uhppoted/uhppoted-breakout/Rev.0/firmware/core/src/sys.c

#include <malloc.h>
#include <stdio.h>
#include <stdlib.h>
#include <string.h>
#include <unistd.h>

#include <hardware/flash.h>
#include <hardware/watchdog.h>
#include <pico/stdlib.h>
#include <pico/sync.h>
#include <pico/unique_id.h>

#include <RTC.h>
#include <SSMP.h>
#include <U2.h>
#include <U3.h>
#include <breakout.h>
#include <cli.h>
#include <log.h>
#include <mempool.h>
#include <settings.h>
#include <sys.h>
#include <types/buffer.h>

#define LOGTAG "SYS"
#define PRINT_QUEUE_SIZE 64

extern const char *TERMINAL_QUERY_STATUS;
const int32_t FLUSH = 1000;              // ms
const uint32_t MODE_CLI_TIMEOUT = 15000; // ms

const uint32_t MSG = 0xf0000000;
const uint32_t MSG_DEBUG = 0x00000000;
const uint32_t MSG_WIO = 0x10000000;
const uint32_t MSG_SWIPE = 0x20000000;
const uint32_t MSG_KEYCODE = 0x30000000;
const uint32_t MSG_U3 = 0x40000000;
const uint32_t MSG_RX = 0x50000000;
const uint32_t MSG_SAVE = 0x60000000;
const uint32_t MSG_EVENT = 0x70000000;
const uint32_t MSG_TTY = 0xb0000000;
const uint32_t MSG_TRACE = 0xc0000000;
const uint32_t MSG_LOG = 0xd0000000;
const uint32_t MSG_WATCHDOG = 0xe0000000;
const uint32_t MSG_TICK = 0xf0000000;

extern queue_t queue;

extern struct {
    queue_t queue;
    mutex_t guard;
} I2C0;

extern void syserr_tick();

struct {
    repeating_timer_t timer;
    uint32_t ticks;
    mode mode;
    bool reboot;

    struct {
        mutex_t lock;
        bool connected;
        int head;
        int tail;
        char list[PRINT_QUEUE_SIZE][128];
    } queue;

    struct {
        absolute_time_t touched;
    } cli;

    struct {
        bool RTC;
        float interval;
        absolute_time_t touched;
        repeating_timer_t timer;
    } trace;

    mutex_t guard;
} SYSTEM = {
    .ticks = 0,
    .mode = MODE_NONE,
    .reboot = false,
    .queue = {
        .connected = false,
        .head = 0,
        .tail = 0,
    },

    .cli = {
        .touched = 0,
    },

    .trace = {
        .RTC = true,
        .interval = (float)TRACE,
        .touched = 0,
    },
};

void _push(const char *);
void _flush();
void _print(const char *);
bool _tick(repeating_timer_t *t);
bool _trace(repeating_timer_t *t);

bool sysinit() {
    mutex_init(&SYSTEM.guard);
    mutex_init(&SYSTEM.queue.lock);

    // ... restore settings
    // FIXME settings_restore();

    // ... USB/UART0 mode
    if (strcasecmp(MODE, "cli") == 0) {
        SYSTEM.mode = MODE_UNKNOWN; // NTS: will be set to MODE_CLI if/when terminal is connected
    } else if (strcasecmp(MODE, "log") == 0) {
        SYSTEM.mode = MODE_LOG;
    } else {
        SYSTEM.mode = MODE_NONE;
    }

    // ... system tick
    if (!add_repeating_timer_ms(1000, _tick, &SYSTEM, &SYSTEM.timer)) {
        return false;
    }

    // ... tracing
    if (!add_repeating_timer_ms(250, _trace, &SYSTEM, &SYSTEM.trace.timer)) {
        return false;
    }

    return true;
}

bool _tick(repeating_timer_t *t) {
    SYSTEM.ticks++;

    message qmsg = {
        .message = MSG_TICK,
        .tag = MESSAGE_NONE,
    };

    push(qmsg);
    syserr_tick();

    return true;
}

bool _trace(repeating_timer_t *t) {
    message m = {
        .message = MSG_TRACE,
        .tag = MESSAGE_NONE,
    };

    push(m);

    return true;
}

/* Checks memory usage, etc.
 *
 */
void syscheck() {
    // ... check memory usage
    uint32_t heap = get_total_heap();
    uint32_t available = get_free_heap();
    float used = 1.0 - ((float)available / (float)heap);

    if (used > 0.5 && !syserr_get(ERR_MEMORY)) {
        syserr_set(ERR_MEMORY, LOGTAG, "memory usage %d%%", (int)(100.0 * used));
    }

    // ... kick watchdog
    if (!SYSTEM.reboot) {
        message qmsg = {
            .message = MSG_WATCHDOG,
            .tag = MESSAGE_NONE,
        };

        push(qmsg);
    }
}

/* Sets sys.reboot flag to inhibit watchdog reset.
 *
 */
void sys_reboot() {
    SYSTEM.reboot = true;
}

void sys_trace() {
    int64_t interval = (int64_t)(1000.0 * SYSTEM.trace.interval);
    absolute_time_t now = get_absolute_time();
    int64_t delta = absolute_time_diff_us(SYSTEM.trace.touched, now) / 1000;

    if (interval > 0 && delta >= interval) {
        uint16_t errors = syserr_bitmask();
        uint32_t heap = get_total_heap();
        uint32_t available = get_free_heap();
        float used = 1.0 - ((float)available / (float)heap);
        const char *watchdogged = syserr_get(ERR_WATCHDOG) ? "** watchdog **" : "";

        debugf(LOGTAG, "trace  ticks:%-5u queue:%u  I2C0:%u  heap:%u  heap:%u  used:%.1f%%  errors:%04x  %s",
               SYSTEM.ticks,
               queue_get_level(&queue),
               queue_get_level(&I2C0.queue),
               heap,
               available,
               100.0f * used,
               errors,
               watchdogged);

        SYSTEM.trace.touched = get_absolute_time();
    }
}

int sys_id(char *ID, int N) {
    pico_unique_board_id_t board_id;

    pico_get_unique_board_id(&board_id);

    snprintf(ID, N, "%02x%02x%02x%02x%02x%02x%02x%02x",
             board_id.id[0],
             board_id.id[1],
             board_id.id[2],
             board_id.id[3],
             board_id.id[4],
             board_id.id[5],
             board_id.id[6],
             board_id.id[7]);

    return N < 16 ? N : 16;
}

mode get_mode() {
    switch (SYSTEM.mode) {
    case MODE_NONE:
        return MODE_NONE;

    case MODE_LOG:
        return MODE_LOG;

    case MODE_CLI:
        return MODE_CLI;

    case MODE_UNKNOWN:
        return MODE_UNKNOWN;

    default:
        return MODE_NONE;
    }
}

void set_mode(mode mode) {
    if (SYSTEM.mode == MODE_NONE) {
        return;
    }

    if (SYSTEM.mode != mode) {
        SYSTEM.mode = mode;

        // ... unblock queue
        if (mode == MODE_CLI) {
            SYSTEM.cli.touched = get_absolute_time();
            print("");
        }
    }
}

void stdout_connected(bool connected) {
    if (connected != SYSTEM.queue.connected) {
        SYSTEM.queue.connected = connected;
        if (connected) {
            print("");
        }
    }
}

void set_trace(float interval) {
    if (interval >= 0.0 && interval <= 300.0) {
        SYSTEM.trace.interval = interval;
    }
}

void set_trace_RTC(bool enabled) {
    SYSTEM.trace.RTC = enabled;
}

void dispatch(uint32_t v) {
    if ((v & MSG) == MSG_DEBUG) {
        debugf(LOGTAG, "... debug??");
    }

    if ((v & MSG) == MSG_WIO) {
        U2_wio(v & 0x0000ffff);
    }

    if ((v & MSG) == MSG_SWIPE) {
        swipe *swipe = (struct swipe *)(SRAM_BASE | (v & 0x0fffffff));

        infof(LOGTAG, "READER %d  CARD %s", swipe->door, swipe->card);

        switch (swipe->door) {
        case 1:
            SSMP_trap(EVENT_DOOR_1_SWIPE, swipe->card);
            break;

        case 2:
            SSMP_trap(EVENT_DOOR_2_SWIPE, swipe->card);
            break;

        case 3:
            SSMP_trap(EVENT_DOOR_3_SWIPE, swipe->card);
            break;

        case 4:
            SSMP_trap(EVENT_DOOR_4_SWIPE, swipe->card);
            break;
        }

        swipe_free(swipe);
    }

    if ((v & MSG) == MSG_KEYCODE) {
        swipe *swipe = (struct swipe *)(SRAM_BASE | (v & 0x0fffffff));

        infof(LOGTAG, "KEYPAD %d  KEYCODE %s", swipe->door, swipe->code);

        switch (swipe->door) {
        case 1:
            SSMP_trap(EVENT_DOOR_1_KEYCODE, swipe->code);
            break;

        case 2:
            SSMP_trap(EVENT_DOOR_2_KEYCODE, swipe->code);
            break;

        case 3:
            SSMP_trap(EVENT_DOOR_3_KEYCODE, swipe->code);
            break;

        case 4:
            SSMP_trap(EVENT_DOOR_4_KEYCODE, swipe->code);
            break;
        }

        swipe_free(swipe);
    }

    if ((v & MSG) == MSG_U3) {
        U3_process(v & 0x000000ff);
    }

    if ((v & MSG) == MSG_RX) {
        struct circular_buffer *b = (struct circular_buffer *)(SRAM_BASE | (v & 0x0fffffff));

        SSMP_rx(b);
    }

    if ((v & MSG) == MSG_TTY) {
        struct circular_buffer *b = (struct circular_buffer *)(SRAM_BASE | (v & 0x0fffffff));

        cli_rx(b);
    }

    if ((v & MSG) == MSG_SAVE) {
        settings_save();
    }

    if ((v & MSG) == MSG_TRACE) {
        sys_trace();

        if (SYSTEM.trace.RTC) {
            RTC_trace();
        }
    }

    if ((v & MSG) == MSG_TICK) {
        syscheck();
        sys_tick();

        // ... MODE_CLI timeout?
        if (get_mode() == MODE_CLI || get_mode() == MODE_UNKNOWN) {
            absolute_time_t now = get_absolute_time();
            int64_t delta = absolute_time_diff_us(SYSTEM.cli.touched, now) / 1000;

            if (llabs(delta) > MODE_CLI_TIMEOUT) {
                set_mode(MODE_UNKNOWN);
            }

            // ... ping terminal
            if (mutex_try_enter(&SYSTEM.guard, NULL)) {
                _print(TERMINAL_QUERY_STATUS);
                mutex_exit(&SYSTEM.guard);
            }
        }

        // ... bump log queue
        message qmsg = {
            .message = MSG_LOG,
            .tag = MESSAGE_NONE,
        };

        push(qmsg);
    }

    if ((v & MSG) == MSG_EVENT) {
        EVENT event = (EVENT)(v & 0x0fffffff);

        SSMP_trap(event, NULL);
    }

    if ((v & MSG) == MSG_LOG) {
        _flush();
    }

    if ((v & MSG) == MSG_WATCHDOG) {
        watchdog_update();
    }
}

void print(const char *msg) {
    switch (SYSTEM.mode) {
    case MODE_NONE:
        return;

    default:
        _push(msg);
    }
}

void _push(const char *msg) {
    if (mutex_try_enter(&SYSTEM.queue.lock, NULL)) {
        int head = SYSTEM.queue.head;
        int tail = SYSTEM.queue.tail;
        int next = (head + 1) % PRINT_QUEUE_SIZE;

        if (next == SYSTEM.queue.tail) {
            snprintf(SYSTEM.queue.list[tail++], 128, "...\n");
            tail %= PRINT_QUEUE_SIZE;

            snprintf(SYSTEM.queue.list[tail], 128, "...\n");

            SYSTEM.queue.tail = tail;
        }

        if (next != SYSTEM.queue.tail) {
            snprintf(SYSTEM.queue.list[head], 128, "%s", msg);
            SYSTEM.queue.head = next;
        }

        mutex_exit(&SYSTEM.queue.lock);
    }

    message qmsg = {
        .message = MSG_LOG,
        .tag = MESSAGE_NONE,
    };

    push(qmsg);
}

/* Flushes all pending messages to stdout.
 *
 */
void _flush() {
    if (SYSTEM.mode != MODE_LOG && SYSTEM.mode != MODE_CLI) {
        return;
    }

    if (SYSTEM.mode != MODE_LOG && SYSTEM.mode != MODE_CLI) {
        return;
    }

    if (!SYSTEM.queue.connected) {
        return;
    }

    if (mutex_try_enter(&SYSTEM.guard, NULL)) {
        if (mutex_try_enter(&SYSTEM.queue.lock, NULL)) {
            int head = SYSTEM.queue.head;
            int tail = SYSTEM.queue.tail;

            while (tail != head) {
                _print(SYSTEM.queue.list[tail++]);
                tail %= PRINT_QUEUE_SIZE;
            }

            SYSTEM.queue.tail = tail;
            mutex_exit(&SYSTEM.queue.lock);
        }

        mutex_exit(&SYSTEM.guard);
    }
}

/* Prints all of a message to stdout.
 *
 */
void _print(const char *msg) {
    int remaining = strlen(msg);
    int ix = 0;
    int N;

    while (remaining > 0) {
        if ((N = fwrite(&msg[ix], 1, remaining, stdout)) <= 0) {
            break;
        } else {
            remaining -= N;
            ix += N;
        }
    }

    fflush(stdout);
}

uint32_t get_total_heap() {
    extern char __StackLimit, __bss_end__;

    return &__StackLimit - &__bss_end__;
}

uint32_t get_free_heap() {
    extern char __StackLimit, __bss_end__;

    uint32_t total = &__StackLimit - &__bss_end__;
    struct mallinfo m = mallinfo();

    return total - m.uordblks;
}
