uhppoted/uhppoted-breakout/Rev.0/firmware/core/src/MIB.c

#include <stdio.h>
#include <stdlib.h>
#include <string.h>

#include <crypt/hash/djb2.h>

#include <MIB.h>
#include <RTC.h>
#include <SSMP.h>
#include <U3.h>
#include <U4.h>
#include <breakout.h>
#include <log.h>
#include <sys.h>

#define LOGTAG "MIB"

const struct {
    uint32_t hash;
    char *OID;
} MIB[] = {
    {.hash = HASH_MIB_BOARD_ID, .OID = MIB_BOARD_ID},
    {.hash = HASH_MIB_CONTROLLER_ID, .OID = MIB_CONTROLLER_ID},
    {.hash = HASH_MIB_CONTROLLER_VERSION, .OID = MIB_CONTROLLER_VERSION},
    {.hash = HASH_MIB_CONTROLLER_RELEASED, .OID = MIB_CONTROLLER_RELEASED},
    {.hash = HASH_MIB_CONTROLLER_DATETIME, .OID = MIB_CONTROLLER_DATETIME},
    {.hash = HASH_MIB_CONTROLLER_SYSERROR, .OID = MIB_CONTROLLER_SYSERROR},
    {.hash = HASH_MIB_CONTROLLER_SYSINFO, .OID = MIB_CONTROLLER_SYSINFO},
    {.hash = HASH_MIB_DOORS_1_UNLOCKED, .OID = MIB_DOORS_1_UNLOCKED},
    {.hash = HASH_MIB_DOORS_2_UNLOCKED, .OID = MIB_DOORS_2_UNLOCKED},
    {.hash = HASH_MIB_DOORS_3_UNLOCKED, .OID = MIB_DOORS_3_UNLOCKED},
    {.hash = HASH_MIB_DOORS_4_UNLOCKED, .OID = MIB_DOORS_4_UNLOCKED},
    {.hash = HASH_MIB_DOORS_1_OPEN, .OID = MIB_DOORS_1_OPEN},
    {.hash = HASH_MIB_DOORS_2_OPEN, .OID = MIB_DOORS_2_OPEN},
    {.hash = HASH_MIB_DOORS_3_OPEN, .OID = MIB_DOORS_3_OPEN},
    {.hash = HASH_MIB_DOORS_4_OPEN, .OID = MIB_DOORS_4_OPEN},
    {.hash = HASH_MIB_DOORS_1_BUTTON, .OID = MIB_DOORS_1_BUTTON},
    {.hash = HASH_MIB_DOORS_2_BUTTON, .OID = MIB_DOORS_2_BUTTON},
    {.hash = HASH_MIB_DOORS_3_BUTTON, .OID = MIB_DOORS_3_BUTTON},
    {.hash = HASH_MIB_DOORS_4_BUTTON, .OID = MIB_DOORS_4_BUTTON},
};

value MIB_get_boolean(const char *OID);

int64_t MIB_set_string(const char *OID, const char *s, int length, value *v);

value MIB_get(const char *OID) {
    uint32_t hash = djb2(OID);

    value v = {
        .tag = VALUE_UNKNOWN,
    };

    if (strcmp(OID, MIB_BOARD_ID) == 0) {
        char ID[32];
        int N = sys_id(ID, sizeof(ID));
        slice octets = {
            .capacity = 64,
            .length = N,
            .bytes = (char *)calloc(64, sizeof(uint8_t)),
        };

        memmove(octets.bytes, ID, N);

        v.tag = VALUE_OCTET_STRING;
        v.octets = octets;
    }

    if (strcmp(OID, MIB_CONTROLLER_ID) == 0) {
        v.tag = VALUE_UINT32;
        v.integer = CONTROLLER;
    }

    if (strcmp(OID, MIB_CONTROLLER_VERSION) == 0) {
        v.tag = VALUE_UINT16;
        v.integer = VERSION;
    }

    if (strcmp(OID, MIB_CONTROLLER_RELEASED) == 0) {
        slice octets = {
            .capacity = 32,
            .length = 0,
            .bytes = (char *)calloc(32, sizeof(uint8_t)),
        };

        int N = snprintf(octets.bytes, octets.capacity, "%s", RELEASED);
        if (N > 0) {
            octets.length = N < strlen(RELEASED) ? N : strlen(RELEASED);
        }

        v.tag = VALUE_OCTET_STRING;
        v.octets = octets;
    }

    if (strcmp(OID, MIB_CONTROLLER_DATETIME) == 0) {
        slice octets = {
            .capacity = 32,
            .length = 0,
            .bytes = (char *)calloc(32, sizeof(uint8_t)),
        };

        char date[16] = {0};
        char time[16] = {0};
        char datetime[32] = {0};

        RTC_get_date(date, sizeof(date));
        RTC_get_time(time, sizeof(time));

        snprintf(datetime, sizeof(datetime), "%s %s", date, time);

        int N = snprintf(octets.bytes, octets.capacity, "%s", datetime);
        if (N > 0) {
            octets.length = N < strlen(datetime) ? N : strlen(datetime);
        }

        v.tag = VALUE_OCTET_STRING;
        v.octets = octets;
    }

    if (strcmp(OID, MIB_CONTROLLER_SYSERROR) == 0) {
        v.tag = VALUE_UINT8;
        v.integer = (uint8_t)get_errors();
    }

    if (strcmp(OID, MIB_CONTROLLER_SYSINFO) == 0) {
        v.tag = VALUE_UINT8;
        v.integer = 0;
    }

    if (strcmp(OID, MIB_DOORS_1_UNLOCKED) == 0) {
        return MIB_get_boolean(OID);
    }

    if (strcmp(OID, MIB_DOORS_2_UNLOCKED) == 0) {
        return MIB_get_boolean(OID);
    }

    if (strcmp(OID, MIB_DOORS_3_UNLOCKED) == 0) {
        return MIB_get_boolean(OID);
    }

    if (strcmp(OID, MIB_DOORS_4_UNLOCKED) == 0) {
        return MIB_get_boolean(OID);
    }

    if (strcmp(OID, MIB_DOORS_1_OPEN) == 0) {
        return MIB_get_boolean(OID);
    }

    if (strcmp(OID, MIB_DOORS_2_OPEN) == 0) {
        return MIB_get_boolean(OID);
    }

    if (strcmp(OID, MIB_DOORS_3_OPEN) == 0) {
        return MIB_get_boolean(OID);
    }

    if (strcmp(OID, MIB_DOORS_4_OPEN) == 0) {
        return MIB_get_boolean(OID);
    }

    if (strcmp(OID, MIB_DOORS_1_BUTTON) == 0) {
        return MIB_get_boolean(OID);
    }

    if (strcmp(OID, MIB_DOORS_2_BUTTON) == 0) {
        return MIB_get_boolean(OID);
    }

    if (strcmp(OID, MIB_DOORS_3_BUTTON) == 0) {
        return MIB_get_boolean(OID);
    }

    if (strcmp(OID, MIB_DOORS_4_BUTTON) == 0) {
        return MIB_get_boolean(OID);
    }

    return v;
}

value MIB_get_boolean(const char *OID) {
    value v = {
        .tag = VALUE_NULL,
    };

    if (strcmp(OID, MIB_DOORS_1_UNLOCKED) == 0) {
        v.tag = VALUE_BOOLEAN;
        v.boolean = U4_get_relay(1);
    }

    if (strcmp(OID, MIB_DOORS_2_UNLOCKED) == 0) {
        v.tag = VALUE_BOOLEAN;
        v.boolean = U4_get_relay(2);
    }

    if (strcmp(OID, MIB_DOORS_3_UNLOCKED) == 0) {
        v.tag = VALUE_BOOLEAN;
        v.boolean = U4_get_relay(3);
    }

    if (strcmp(OID, MIB_DOORS_4_UNLOCKED) == 0) {
        v.tag = VALUE_BOOLEAN;
        v.boolean = U4_get_relay(4);
    }

    if (strcmp(OID, MIB_DOORS_1_OPEN) == 0) {
        v.tag = VALUE_BOOLEAN;
        v.boolean = U3_get_door(1);
    }

    if (strcmp(OID, MIB_DOORS_2_OPEN) == 0) {
        v.tag = VALUE_BOOLEAN;
        v.boolean = U3_get_door(2);
    }

    if (strcmp(OID, MIB_DOORS_3_OPEN) == 0) {
        v.tag = VALUE_BOOLEAN;
        v.boolean = U3_get_door(3);
    }

    if (strcmp(OID, MIB_DOORS_4_OPEN) == 0) {
        v.tag = VALUE_BOOLEAN;
        v.boolean = U3_get_door(4);
    }

    if (strcmp(OID, MIB_DOORS_1_BUTTON) == 0) {
        v.tag = VALUE_BOOLEAN;
        v.boolean = U3_get_button(1);
    }

    if (strcmp(OID, MIB_DOORS_2_BUTTON) == 0) {
        v.tag = VALUE_BOOLEAN;
        v.boolean = U3_get_button(2);
    }

    if (strcmp(OID, MIB_DOORS_3_BUTTON) == 0) {
        v.tag = VALUE_BOOLEAN;
        v.boolean = U3_get_button(3);
    }

    if (strcmp(OID, MIB_DOORS_4_BUTTON) == 0) {
        v.tag = VALUE_BOOLEAN;
        v.boolean = U3_get_button(4);
    }

    // FIXME return error ?

    return v;
}

int64_t MIB_set(const char *OID, const value u, value *v) {
    switch (u.tag) {
    case VALUE_OCTET_STRING:
        return MIB_set_string(OID, u.octets.bytes, u.octets.length, v);
        break;

    case VALUE_NULL:
        warnf(LOGTAG, "set - NULL value");
        return SSMP_ERROR_BAD_VALUE;

    default:
        warnf(LOGTAG, "set - unknown value type (%d)", u.tag);
        return SSMP_ERROR_BAD_VALUE;
    }
}

int64_t MIB_set_string(const char *OID, const char *s, int length, value *v) {
    if (strcmp(OID, MIB_CONTROLLER_DATETIME) == 0) {
        int year;
        int month;
        int day;
        int hour;
        int minute;
        int second;
        int rc;

        if ((rc = sscanf(s, "%04d-%02d-%02d %02d:%02d:%02d", &year, &month, &day, &hour, &minute, &second)) != 6) {
            return SSMP_ERROR_BAD_VALUE;
        } else if (!RTC_set_date(year, month, day)) {
            warnf(LOGTAG, "error setting RTC date %04d-%02d-%02d", year, month, day);
            return SSMP_ERROR_COMMIT_FAILED;
        } else if (!RTC_set_time(hour, minute, second)) {
            warnf(LOGTAG, "error setting RTC time %02d:%02d:%02d", hour, minute, second);
            return SSMP_ERROR_COMMIT_FAILED;
        }

        slice octets = {
            .capacity = 32,
            .length = 0,
            .bytes = (char *)calloc(32, sizeof(uint8_t)),
        };

        // NTS: RTC is not updated immediately
        // char date[16] = {0};
        // char time[16] = {0};
        // char datetime[32] = {0};
        //
        // RTC_get_date(date, sizeof(date));
        // RTC_get_time(time, sizeof(time));
        //
        // snprintf(datetime, sizeof(datetime), "%s %s", date, time);

        int N = snprintf(octets.bytes, octets.capacity, "%04d-%02d-%02d %02d:%02d:%02d", year, month, day, hour, minute, second);
        if (N > 0) {
            octets.length = N;
        }

        v->tag = VALUE_OCTET_STRING;
        v->octets = octets;

        return SSMP_ERROR_NONE;
    }

    return SSMP_ERROR_NO_SUCH_OBJECT;
}
