uhppoted/uhppoted-breakout/Rev.0/firmware/core/src/usb.c

#include <tusb.h>

#include <breakout.h>
#include <log.h>
#include <sys.h>
#include <types/buffer.h>
#include <usb.h>

#define LOGTAG "USB"

const uint8_t CDC1 = 1;

struct {
    repeating_timer_t usb_timer;

    struct {
        circular_buffer cli;
        circular_buffer ssmp;
    } buffers;

    struct {
        bool usb0;
        bool usb1;
    } connected;

    struct {
        mutex_t usb0;
        mutex_t usb1;
    } guard;
} USB = {
    .buffers = {
        .cli = {
            .head = 0,
            .tail = 0,
        },

        .ssmp = {
            .head = 0,
            .tail = 0,
        },
    },

    .connected = {
        .usb0 = false,
        .usb1 = false,
    },
};

bool usb_tick(repeating_timer_t *rt);

bool usb_init() {
    USB.connected.usb0 = false;
    USB.connected.usb1 = false;

    mutex_init(&USB.guard.usb0);
    mutex_init(&USB.guard.usb1);

    add_repeating_timer_ms(25, usb_tick, NULL, &USB.usb_timer);

    infof(LOGTAG, "initialised");

    return true;
}

bool usb_tick(repeating_timer_t *rt) {
    if (tud_cdc_n_connected(0) && !USB.connected.usb0) {
        USB.connected.usb0 = true;

        infof(LOGTAG, "USB.0 connected");
        stdout_connected(true);
    } else if (!tud_cdc_n_connected(0) && USB.connected.usb0) {
        USB.connected.usb0 = false;

        infof(LOGTAG, "USB.0 disconnected");
        stdout_connected(false);
    }

    if (tud_cdc_n_connected(1) && !USB.connected.usb1) {
        USB.connected.usb1 = true;

        infof(LOGTAG, "USB.1 connected");
    } else if (!tud_cdc_n_connected(1) && USB.connected.usb1) {
        USB.connected.usb1 = false;

        infof(LOGTAG, "USB.1 disconnected");
    }

    tud_task();

    return true;
}

// Synchronous write (USB.1 only - use stdout for USB.0).
//
// NTS: sadly buffered write introduces a world of complication - partial
//      messages, the poll loop has to run faster, messages get sent in drips
//      and drabs, etc, etc. A synchronous write doesn't really cost anything
//      here because SSMP is processing a request anyway.
//
// NTS: retries don't seem to be necessary - leaving in for the interim.
bool usb1_write(const uint8_t *bytes, int len) {
    int retries = 0;
    bool ok = true;

    mutex_enter_blocking(&USB.guard.usb1);

    if (USB.connected.usb1) {
        for (int ix = 0; ix < len;) {
            uint32_t N = tud_cdc_n_write(CDC1, &bytes[ix], len - ix);

            if (N == 0 && retries > 5) {
                warnf(LOGTAG, "*** write error %u of %d", ix, len);
                ok = false;
                break;
            } else if (N == 0) {
                retries++;
                sleep_ms(1);
                tud_task();
            } else {
                tud_cdc_n_write_flush(CDC1);

                debugf(LOGTAG, "write %u of %d", N, len - ix);
                ix += N;
                retries = 0;
            }
        }
    } else {
        ok = false;
        warnf(LOGTAG, "write error: USB not connected");
    }

    mutex_exit(&USB.guard.usb1);

    return ok;
}

// tinyusb callback for received data
void tud_cdc_rx_cb(uint8_t itf) {
    uint8_t buf[CFG_TUD_CDC_RX_BUFSIZE];

    // NB: also do this for CDC0 because otherwise you won't be able to
    //     print anymore to CDC0 next time this function is called
    uint32_t count = tud_cdc_n_read(itf, buf, sizeof(buf));

    // USB.0 ?
    if (itf == 0 && count > 0) {
        for (int i = 0; i < count; i++) {
            buffer_push(&USB.buffers.cli, buf[i]);
        }

        message qmsg = {
            .message = MSG_TTY,
            .tag = MESSAGE_BUFFER,
            .buffer = &USB.buffers.cli,
        };

        push(qmsg);
    }

    // USB.1 ?
    if (itf == 1 && count > 0) {
        for (int i = 0; i < count; i++) {
            buffer_push(&USB.buffers.ssmp, buf[i]);
        }

        message qmsg = {
            .message = MSG_RX,
            .tag = MESSAGE_BUFFER,
            .buffer = &USB.buffers.ssmp,
        };

        push(qmsg);
    }
}
