uhppoted/uhppoted-breakout/Rev.0/firmware/core/include/sys.h

#pragma once

#include <pico/time.h>

typedef enum {
    MODE_NONE,
    MODE_LOG,
    MODE_CLI,
    MODE_UNKNOWN,
} mode;

extern bool sys_init();
extern void sys_tick();
extern void sys_trace();
extern void sys_reboot();
extern int sys_id(char *ID, int N);

extern void syscheck();
extern void dispatch(uint32_t);

extern void print(const char *);
extern mode get_mode();
extern void set_mode(mode);
extern void stdout_connected(bool);
extern void set_trace(float interval);
extern void set_trace_RTC(bool enabled);

extern uint32_t get_total_heap();
extern uint32_t get_free_heap();
