uhppoted/uhppoted-breakout/Rev.0/firmware/core/include/log.h

#pragma once

void log_init();

void debugf(const char *tag, const char *fmt, ...);
void infof(const char *tag, const char *fmt, ...);
void warnf(const char *tag, const char *fmt, ...);
void errorf(const char *tag, const char *fmt, ...);
