uhppoted/uhppoted-breakout/Rev.0/firmware/pico/include/I2C0.h

#pragma once

#include <stdint.h>

extern void I2C0_init();
extern void I2C0_scan();

extern int I2C0_write(uint8_t addr, uint8_t reg, uint8_t data);
extern int I2C0_write_all(uint8_t addr, uint8_t reg, uint8_t data[], int N);
extern int I2C0_read(uint8_t addr, uint8_t reg, uint8_t *data);
extern int I2C0_read_all(uint8_t addr, uint8_t reg, uint8_t *data, int N);
