uhppoted/uhppoted-breakout/Rev.0/firmware/pico/include/breakout.h

#pragma once

#include <pico/util/queue.h>

extern const uint32_t MSG;
extern const uint32_t MSG_RX;

extern const uint I2C0_SDA;
extern const uint I2C0_SCL;

extern const uint U3_RESET;
extern const uint U5;

extern queue_t queue;
